ARTITULE/FlappyINO/src/FlappyBird_Game.cpp

#define BirdGroundPlane 56

#define Low_pipe_HIGH 25
#define Low_pipe_LOW 60
#define Middle_pipe_HIGH 15
#define Middle_pipe_LOW 52
#define Top_pipe_HIGH 5
#define Top_pipe_LOW 42

#include "FlappyBird_Game.h"
#include "bitmap.h"
#include "functions.h"
#include "EEPROM.h"

int8_t Pipe_Collision_Points[2][3] = {
    {
        Low_pipe_HIGH,
        Middle_pipe_HIGH,
        Top_pipe_HIGH,
    },
    {
        Low_pipe_LOW,
        Middle_pipe_LOW,
        Top_pipe_LOW,
    }};

void FBirdGame(int8_t EEPROM_ADDR, int8_t Difficulty, int8_t setting1, int8_t setting2, int8_t setting3, int16_t game_complete_score, GyverOLED<SSD1306_128x64, OLED_BUFFER, OLED_SPI, OLED_CS, OLED_DC, OLED_RST> &oled, Button &main_button) {


    bool wasOnPlanetBefore = false;

StartBirdGame:


    float BirdU = 0.0;
    float BGravity = 0.0;
    int birdY = 20;
    int NumOfFlappedFrames = 0;

    bool BirdFlapp = false;
    bool GameOVER = false;
    bool PipeIsDeadly = false;
    bool SpeedIncreaseText = false;
    bool GravityON = false;
    bool PauseClick = false;
    bool endless = false;
    bool showAnimation = setting1;
    bool showBackground = setting2;
    int8_t showStars = setting3;

    int8_t SpeedStep = 10;
    int8_t GameSpeed = 30;
    int8_t EnemyStep = 1;
    int8_t GspeedInc = 1;
    int8_t increasePipeCounter = 0;

    int16_t PipeCounter = 0;
    int16_t BestScore = 0;
    int16_t gameCompleteScore = game_complete_score;

    int8_t oldPipePos = 128;
    int8_t oldPipeType = 0;
    int8_t newPipePos = 128;
    int8_t newPipeType = random(0, 3);

    int8_t firstBackgroundPos = 0;
    int8_t secondBackgroundPos = 128;
    uint8_t backgroundScrollX = 0; 

    if (showAnimation && wasOnPlanetBefore == false) {
        wasOnPlanetBefore = true;
        landingAnimation(true, oled);
    }
    WaitingScreen(oled);

    startEndless:

    const char* difficulty;

    switch (Difficulty) {
    case 0:
        GameSpeed = 25;
        EnemyStep = 1;
        GspeedInc = 3;
        BGravity = 0.060f;
        difficulty = "STEADY MODE";
        break;

    case 1:
        GameSpeed = 20;
        EnemyStep = 2;
        GspeedInc = 2;
        BGravity = 0.080f;
        difficulty = "RUSH MODE";
        break;

    case 2:
        GameSpeed = 10;
        EnemyStep = 2;
        GspeedInc = 1;
        BGravity = 0.100f;
        difficulty = "FRENZY MODE";
        break;
    }

    EEPROM.get(EEPROM_ADDR, BestScore);

    while (1) {

        /*  ---------------- USER INPUT ----------------  */
        if (!PauseClick){
            main_button.tick();
        }
        

        if (main_button.click()) {
            BirdU = -0.8;
            birdY -= 2;
            NumOfFlappedFrames = 1500;
            if (GravityON == false)
                GravityON = true;
        }

        /*  ---------------- GAME PROCESSING ----------------  */

        switch (PipeCounter) {
        case 10:
            SpeedIncreaseText = true;
            break;
        case 11:
            SpeedStep = 10;
            break;
        case 20:
            SpeedIncreaseText = true;
            break;
        case 21:
            SpeedStep = 20;
            break;
        case 40:
            SpeedIncreaseText = true;
            break;
        case 41:
            SpeedStep = 10;
            break;
        case 50:
            SpeedIncreaseText = true;
            break;
        case 51:
            SpeedStep = 30;
            break;
        case 80:
            SpeedIncreaseText = true;
            break;
        case 81:
            SpeedStep = 20;
            break;
        case 100:
            SpeedIncreaseText = true;
            break;
        case 101:
            SpeedStep = 50;
            break;
        case 150:
            SpeedIncreaseText = true;
            break;
        }

        if (increasePipeCounter / SpeedStep >= 1) {
            GameSpeed -= GspeedInc;
            increasePipeCounter = 0;
        }

        static uint32_t PipeTimer = millis();
        if (millis() - PipeTimer >= GameSpeed) {
            PipeTimer = millis();
            newPipePos -= EnemyStep;

            if (newPipePos <= 12) {
                oldPipePos = newPipePos;
                oldPipeType = newPipeType;
                newPipePos = 128;
                newPipeType = random(0, 3);
                PipeCounter += 1;
                increasePipeCounter += 1;
            }
            if (oldPipePos >= -24) {
                oldPipePos -= EnemyStep;
                if (oldPipePos <= 2) {
                    PipeIsDeadly = false;
                }
                if (oldPipePos > 2) {
                    PipeIsDeadly = true;
                }
            }
        }



        static uint32_t BackgroundTimer = millis();
        if (millis() - BackgroundTimer >= 15) {
            BackgroundTimer = millis();
            backgroundScrollX = (backgroundScrollX + 1) % 64;
            secondBackgroundPos -= 1;
            if (secondBackgroundPos <= 0) {
                firstBackgroundPos = secondBackgroundPos;
                secondBackgroundPos = 128;
            }
            else {
                firstBackgroundPos -= 1;
            }
        }

        static uint32_t FlapTimer = millis();
        if (millis() - FlapTimer >= 400) {
            if (NumOfFlappedFrames != 0) {
                BirdFlapp = true;
                NumOfFlappedFrames -= 1;
            }
            else {
                BirdFlapp = false;
            }
        }

        if (GravityON) {
            static uint32_t BridGravityTimer = millis();
            if (millis() - BridGravityTimer >= 10) {
                BridGravityTimer = millis();

                BirdU += (float)BGravity;
                birdY += (float)BirdU;
            }
        }

        /*  ---------------- DRAWING ----------------  */

        static uint32_t drawTimer = millis();

        if (millis() - drawTimer >= (1000 / GAME_FPS)) {

            drawTimer = millis();
            oled.clear();
            if (setting2) {
                oled.drawBitmap(firstBackgroundPos, 47, bitmap_BackgroundMoon, 128, 16);
                if (secondBackgroundPos != 128) {
                    oled.drawBitmap(secondBackgroundPos, 47, bitmap_BackgroundMoon, 128, 16);
                }
            }
     
            oled.setScale(1);
            oled.setCursorXY(0, 2);
            oled.print("S:");
            oled.print(PipeCounter);
            if (SpeedIncreaseText) {
                oled.clear(0, 55, 42, 63);
                oled.setCursorXY(0, 55);
                oled.print("+ Speed");
                SpeedIncreaseText = false;
            }
            oled.line(0, 0, 127, 0);
            oled.line(0, 63, 127, 63);

            switch (oldPipeType) {
            case 0:
                if (showBackground) {
                    oled.clear(oldPipePos, 63 - 6, oldPipePos + 16, 63 - 1);
                    oled.clear(oldPipePos + 3, 63, oldPipePos + 13, 63);
                }
                oled.drawBitmap(oldPipePos, 0, bitmap__Low_pipe, 16, 64);
                break;
            case 1:
                if (showBackground) {
                    oled.clear(oldPipePos, 63 - 15, oldPipePos + 16, 63 - 10);
                    oled.clear(oldPipePos + 3, 63 - 9, oldPipePos + 13, 63);
                }
                oled.drawBitmap(oldPipePos, 0, bitmap__Middle_pipe, 16, 64);
                break;
            case 2:
                if (showBackground) {
                    oled.clear(oldPipePos, 63 - 26, oldPipePos + 16, 63 - 21);
                    oled.clear(oldPipePos + 3, 63 - 20, oldPipePos + 13, 63);
                }
                oled.drawBitmap(oldPipePos, 0, bitmap__Top_pipe, 16, 64);
                break;
            }

            switch (newPipeType) {
            case 0:
                if (showBackground) {
                    oled.clear(newPipePos, 63 - 6, newPipePos + 16, 63 - 1);
                    oled.clear(newPipePos + 3, 63, newPipePos + 13, 63);
                }
                oled.drawBitmap(newPipePos, 0, bitmap__Low_pipe, 16, 64);
                break;
            case 1:
                if (showBackground) {
                    oled.clear(newPipePos, 63 - 15, newPipePos + 16, 63 - 10);
                    oled.clear(newPipePos + 3, 63 - 9, newPipePos + 13, 63);
                }
                oled.drawBitmap(newPipePos, 0, bitmap__Middle_pipe, 16, 64);
                break;
            case 2:
                if (showBackground) {
                    oled.clear(newPipePos, 63 - 26, newPipePos + 16, 63 - 21);
                    oled.clear(newPipePos + 3, 63 - 20, newPipePos + 13, 63);
                }
                oled.drawBitmap(newPipePos, 0, bitmap__Top_pipe, 16, 64);
                break;
            }

            if (showStars == 1) {

                for (uint8_t i = 0; i < NUM_STARS; i++) {
                    uint8_t sx = pgm_read_byte(&StarX[i]);
                    uint8_t sy = pgm_read_byte(&StarY[i]);
                    // period is 64px, so draw two copies to cover the 128px screen width
                    for (int16_t tile = 0; tile < 128; tile += 64) {
                        int16_t x = ((int16_t)sx - backgroundScrollX + 64) % 64 + tile;
                        if (x >= 0 && x < 128) {
                            oled.dot(x, sy, 1);  // check exact pixel-set method name in GyverOLED — may be .dot(), .point(), or .setPixel()
                        }
                    }
                }
            }

            if (birdY >= BirdGroundPlane or birdY <= -8) {
                GameOVER = true;
            }
            if (PipeCounter > 1) {
                if (birdY < Pipe_Collision_Points[0][oldPipeType] && PipeIsDeadly or birdY + 16 > Pipe_Collision_Points[1][oldPipeType] && PipeIsDeadly) {
                    GameOVER = true;
                }
            }

            if (PipeCounter >= gameCompleteScore && endless == 0) {
                PauseClick = true;
                WaitingScreen(oled);
                showDifficultyClearScreen(difficulty, oled);
                oled.update();
                while (1) {
                    if (PauseClick) {
                        PauseClick = false;
                        for (int8_t i = 0; i < 10; i++) {
                            main_button.tick();
                        }
                    }
                    main_button.tick();
                    if (main_button.click()) {
                        while (1) {
                            static uint8_t menuPointer = 4;
                            main_button.tick();
                            if (main_button.click()) {
                                menuPointer = (menuPointer == 4 ? 7 : 4);
                            }
                            showInfoScreen(difficulty, oled);
                            oled.setCursor(127 - 6, menuPointer);
                            oled.print("<");
                            oled.update();
                            if (main_button.hold()) {
                                switch ((menuPointer)) {
                                case 4:
                                    goto NewScoreScreen;
                                    break;
                            
                                case 7:
                                    PipeIsDeadly = false;
                                    endless = true;
                                    GravityON = false;
                                    WaitingScreen(oled);
                                    goto startEndless;
                                    break;
                                }
                            }
                        }
                        

                    }
                }
            }
            if (GameOVER) {
                PauseClick = true;
                WaitingScreen(oled);
                NewScoreScreen:
                if (PipeCounter > BestScore) {
                    EEPROM.put(EEPROM_ADDR, PipeCounter);
                    BestScore = PipeCounter;
                    oled.clear();
                    printCentered("NEW HIGH", 1 * 8, 2, oled);
                    printCentered("SCORE!", 3 * 8, 2, oled);
                    printCentered(String(BestScore).c_str(), 5 * 8, 3, oled);
                    oled.roundRect(0, 1, 127, 63, OLED_STROKE);
                    oled.update();
                    while (1) {
                        if (PauseClick) {
                            PauseClick = false;
                            for (int8_t i = 0; i < 10; i++){
                                main_button.tick();
        
                            }
                        }
                        main_button.tick();
                        if (main_button.click())
                            goto EndScreen;
                    }
                }
            EndScreen:
                oled.clear();
                oled.roundRect(0, 1, 127, 63, OLED_STROKE);
                printCentered("GAME OVER", 1 * 8, 2, oled);
                oled.setScale(1);
                oled.setCursor(7, 4);
                oled.print("Score : ");
                oled.print(PipeCounter);
                oled.setCursor(7, 6);
                oled.print("Best Score : ");
                oled.print(BestScore);
                oled.update();
                while (1) {
                    if (PauseClick) {
                        PauseClick = false;
                        for (int8_t i = 0; i < 10; i++){
                            main_button.tick();
    
                        }
                    }
                    
                    main_button.tick();
                    if (main_button.click()) {
                        goto StartBirdGame;
                    }

                    if (main_button.hold()) {
                        if (showAnimation) {
                            landingAnimation(false, oled);                            
                        }
                        return;
                    }
                }
            }

            oled.drawBitmap(0, birdY, BirdFlapp ? bitmap__Bird_Flapped : bitmap__Bird_Normal, 16, 16);
            batCheckDraw(oled);
            oled.update();
        }
    }
}
