ARTITULE/FlappyINO/src/bitmap.cpp

#include "bitmap.h"

const uint8_t StarX[NUM_STARS] PROGMEM = {20, 53, 45, 47, 58, 21, 9, 35, 50, 0, 36};
const uint8_t StarY[NUM_STARS] PROGMEM = {1, 6, 8, 22, 20, 26, 33, 37, 44, 61, 56};

// ' Bird_Normal', 16x16px
const unsigned char bitmap__Bird_Normal [] PROGMEM = {
	0x00, 0xc0, 0x20, 0x20, 0x50, 0x88, 0x08, 0x08, 0xe8, 0x18, 0x58, 0xd0, 0x20, 0xc0, 0x00, 0x00, 
	0x00, 0x01, 0x06, 0x0a, 0x0a, 0x0b, 0x10, 0x10, 0x11, 0x16, 0x15, 0x15, 0x15, 0x15, 0x0d, 0x06
};
// ' Bird_Flapped', 16x16px
const unsigned char bitmap__Bird_Flapped [] PROGMEM = {
	0x00, 0xc0, 0x20, 0x20, 0x10, 0x08, 0x08, 0x08, 0xe8, 0x18, 0x58, 0xd0, 0x20, 0xc0, 0x00, 0x00, 
	0x00, 0x1d, 0x22, 0x22, 0x12, 0x0c, 0x10, 0x10, 0x11, 0x16, 0x15, 0x15, 0x15, 0x15, 0x0d, 0x06
};
// ' Background', 64x64px
const uint8_t bitmap__Background[] PROGMEM = {
	0x00, 0x00, 0x00, 0x00, 0x00, 0x00, 0x00, 0x00, 0x00, 0x00, 0x00, 0x00, 0x00, 0x00, 0x00, 0x00, 0x00, 0x00, 0x00, 0x00, 0x02, 0x00, 0x00, 0x00, 
	0x00, 0x00, 0x00, 0x00, 0x00, 0x00, 0x00, 0x00, 0x00, 0x00, 0x00, 0x00, 0x00, 0x00, 0x00, 0x00, 0x00, 0x00, 0x00, 0x00, 0x00, 0x00, 0x00, 0x00, 
	0x00, 0x00, 0x00, 0x00, 0x00, 0x40, 0x00, 0x00, 0x00, 0x00, 0x00, 0x00, 0x00, 0x00, 0x00, 0x00, 0x00, 0x00, 0x00, 0x00, 0x00, 0x00, 0x00, 0x00, 
	0x00, 0x00, 0x00, 0x00, 0x00, 0x00, 0x00, 0x00, 0x00, 0x00, 0x00, 0x00, 0x00, 0x00, 0x00, 0x00, 0x00, 0x00, 0x00, 0x00, 0x00, 0x00, 0x00, 0x00, 
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
	0x00, 0x00, 0x00, 0x00, 0x04, 0x0b, 0x12, 0x12, 0x12, 0x64, 0x44, 0x24, 0x24, 0x24, 0x24, 0x48, 0x08, 0x08, 0x08, 0x08, 0x48, 0x48, 0x48, 0x48, 
	0x48, 0x48, 0x48, 0x08, 0x08, 0x08, 0x08, 0x08, 0x48, 0x48, 0x24, 0x24, 0x24, 0x44, 0x44, 0x24, 0x12, 0x12, 0x12, 0x0b, 0x04, 0x00, 0x00, 0x00
};

const uint8_t bitmap_LandingPadArm[] PROGMEM = {
	0x06, 0xf9, 0xb9, 0x49, 0xb9, 0xf9, 0x09, 0x05, 0x05, 0x03, 0x00, 0x00, 0x00, 0x00, 0x00, 0x00, 0x00, 0xff, 0x6d, 0x92, 0x6d, 0xff, 0x00, 0x00, 
	0x00, 0x00, 0x00, 0x00, 0x00, 0x00, 0x00, 0x00, 0x00, 0xff, 0xdb, 0x24, 0xdb, 0x3f, 0xa0, 0xa0, 0xa0, 0xa0, 0xa0, 0xa0, 0xa0, 0x20, 0xa0, 0x00, 
	0x00, 0xff, 0xb6, 0x49, 0xb6, 0xff, 0xc0, 0x60, 0x30, 0x18, 0x0c, 0x06, 0x03, 0x01, 0x00, 0x00, 0x00, 0xff, 0x6d, 0x92, 0x6d, 0xff, 0x00, 0x00, 
	0x00, 0x00, 0x00, 0x00, 0x00, 0x00, 0x00, 0x00, 0x60, 0x7f, 0x67, 0x44, 0x67, 0x7f, 0x60, 0x40, 0x00, 0x00, 0x00, 0x00, 0x00, 0x00, 0x00, 0x00
};
