ARTITULE/FlappyINO/src/bitmap.h

#ifndef BITMAPS_H
#define BITMAPS_H

#include <Arduino.h> 

#define NUM_STARS 11

extern const uint8_t StarX[NUM_STARS] PROGMEM;
extern const uint8_t StarY[NUM_STARS] PROGMEM;
extern const unsigned char bitmap__Bird_Normal [] PROGMEM;
extern const unsigned char bitmap__Bird_Flapped [] PROGMEM;
extern const uint8_t bitmap__Background[] PROGMEM;
extern const uint8_t bitmap_BackgroundMoon[] PROGMEM;
extern const uint8_t bitmap__FlappyBirdLogo[] PROGMEM;
extern const uint8_t bitmap__Low_pipe[] PROGMEM;
extern const uint8_t bitmap__Middle_pipe[] PROGMEM;
extern const uint8_t bitmap__Top_pipe[] PROGMEM;
extern const uint8_t bitmap_Moon[] PROGMEM;
extern const uint8_t bitmap_Earth[] PROGMEM;
extern const uint8_t bitmap_Jupiter[] PROGMEM;
extern const uint8_t bitmap_Saturn[] PROGMEM;
extern const uint8_t bitmap_verticalPattern[] PROGMEM;
extern const uint8_t bitmap_Trophy[] PROGMEM;
extern const uint8_t bitmap_lockClosed[] PROGMEM;
extern const uint8_t bitmap_lockOpen[] PROGMEM;
extern const uint8_t bitmap_Spaceship[] PROGMEM;
extern const uint8_t bitmap_Fire[] PROGMEM;
extern const uint8_t bitmap_LandingPad[] PROGMEM;
extern const uint8_t bitmap_LandingPadArm[] PROGMEM;


#endif
